cyx3705/2025-015/b-Picture/电器参考原理图.png

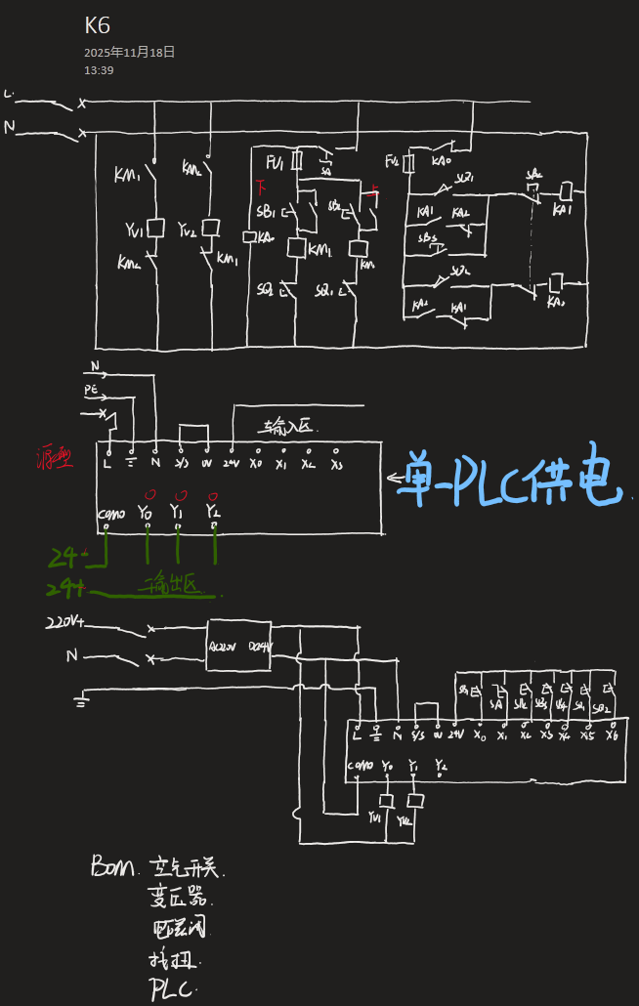
b-Picture/电器参考原理图.png
