cyx3705/2025-015/b-Picture/第三次作业图片记录 .png

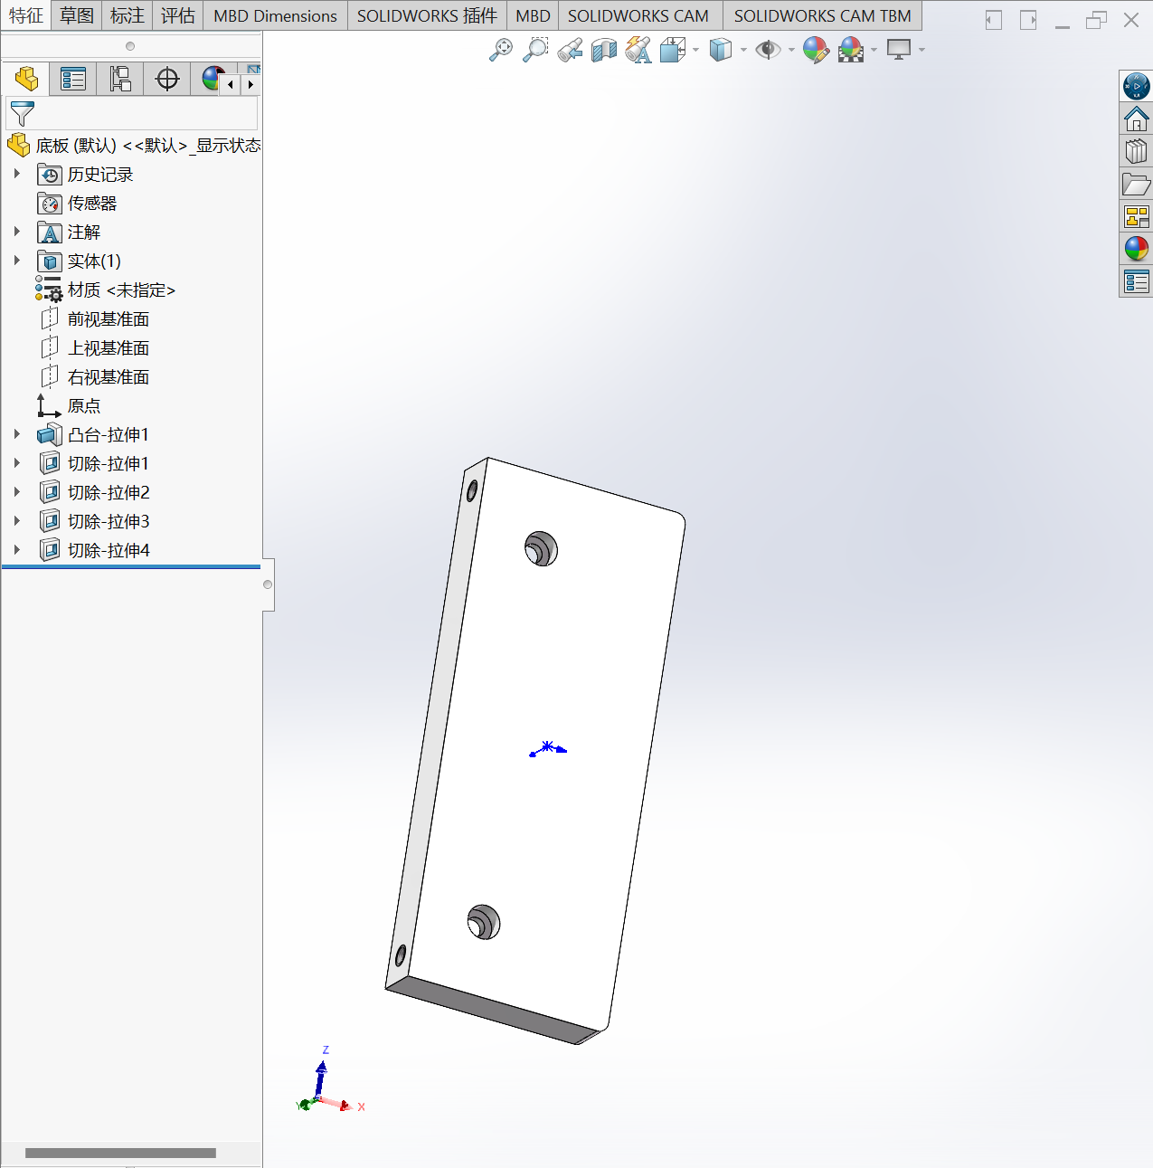
b-Picture/第三次作业图片记录 .png
