cyx3705/2025-015/b-Picture/第五次作业图片记录 (1).png

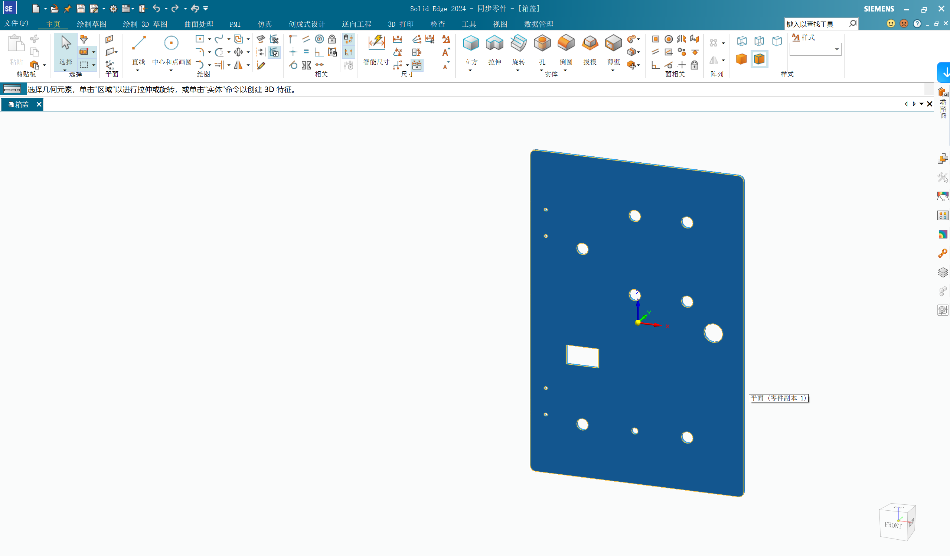
b-Picture/第五次作业图片记录 (1).png
