cyx3705/2025-015/b-Module-GE/按钮/NP2-BW1按钮三维模型202204.stp

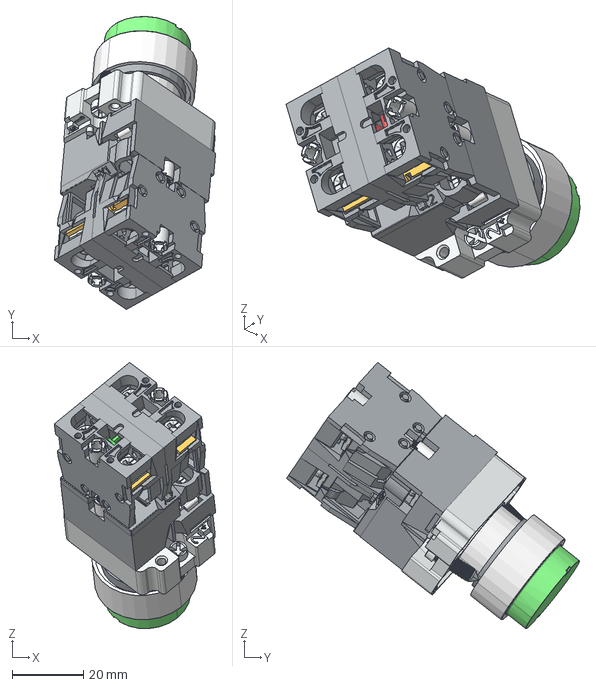
[picture p36: CAD file, 2026-09-21]
b-Module-GE/按钮/NP2-BW1按钮三维模型202204.stp
45.5 x 82.5 x 75.0 mm
