cyx3705/2025-015/b-Module-GE/配件箱/箱体.stp

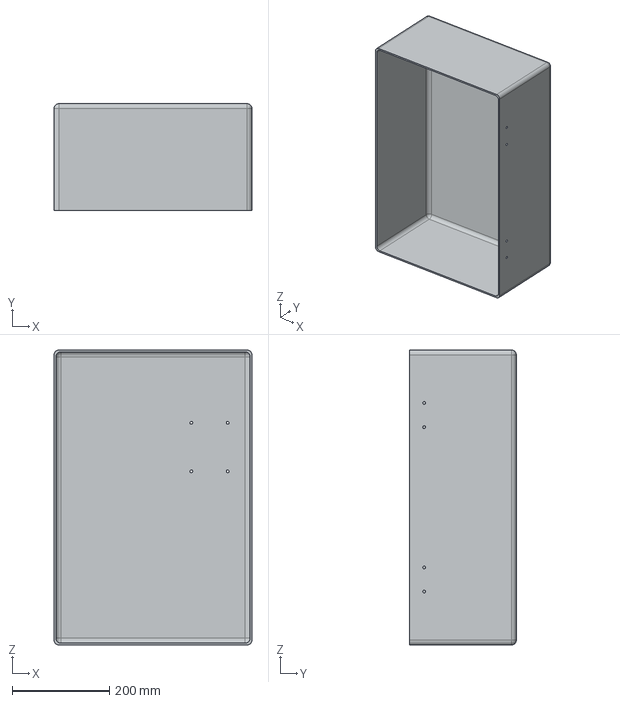
[picture p37: CAD file, 2026-09-21]
b-Module-GE/配件箱/箱体.stp
408.0 x 220.0 x 608.0 mm
