cyx3705/2025-015/b-Module-GE/零件1.stp

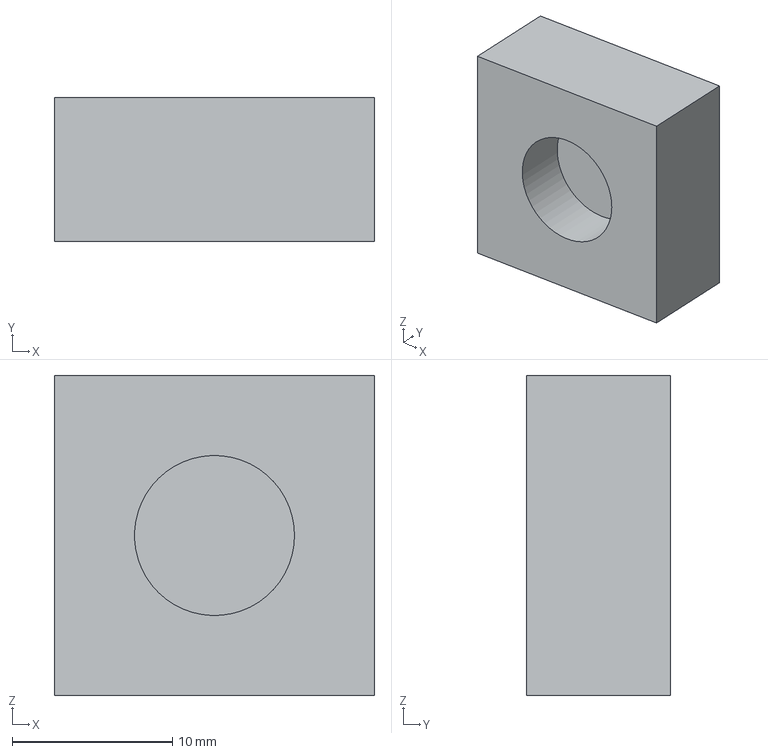
[picture p38: CAD file, 2026-09-21]
b-Module-GE/零件1.stp
20.0 x 9.00 x 20.0 mm
