cyx3705/2025-015/b-Module-SW/主体/背板.SLDPRT

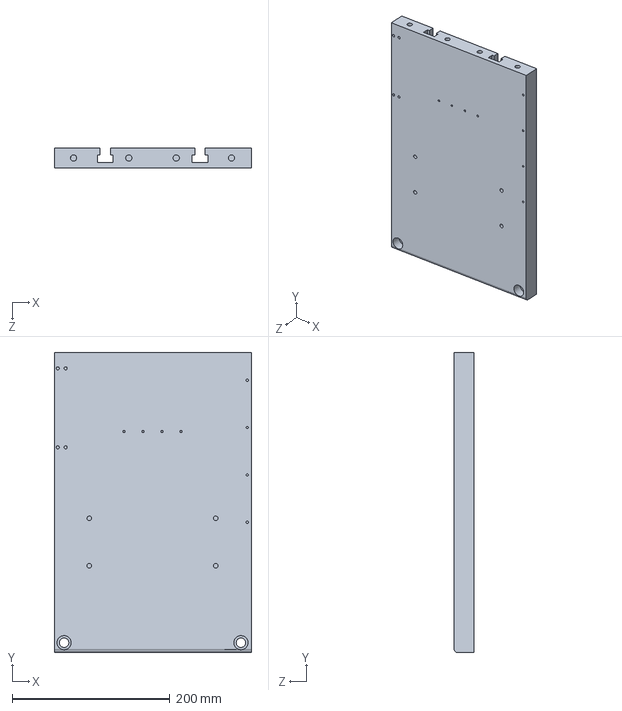
[picture p39: CAD file, 2026-05-30]
b-Module-SW/主体/背板.SLDPRT
250.0 x 380.0 x 25.0 mm
