cyx3705/2025-015/b-Module-GE/主体/光轴.STEP

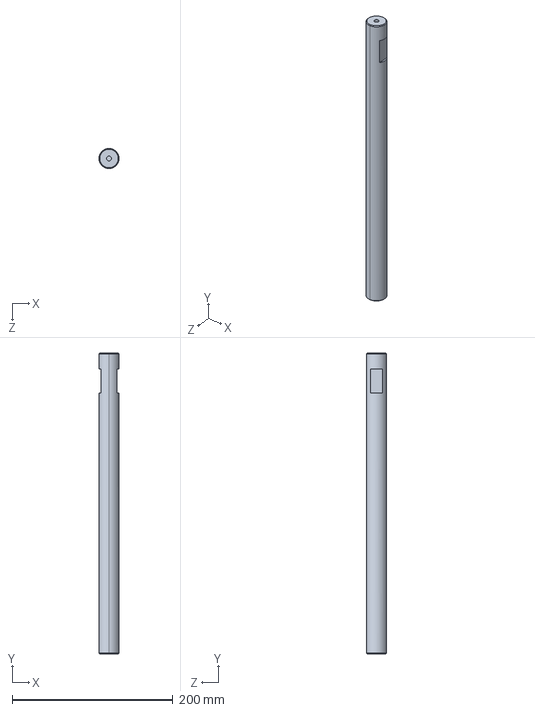
[picture p40: CAD file, 2026-09-21]
b-Module-GE/主体/光轴.STEP
25.0 x 375.0 x 25.0 mm
