cyx3705/2025-015/b-Module-GE/按钮/NP2-BW4按钮三维模型202204.stp

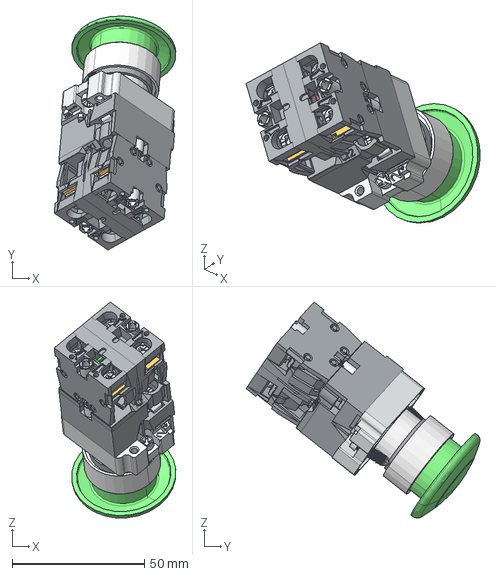
[picture p41: CAD file, 2026-09-21]
b-Module-GE/按钮/NP2-BW4按钮三维模型202204.stp
45.9 x 88.3 x 81.5 mm
