cyx3705/2025-015/b-Module-GE/触碰开关.stp

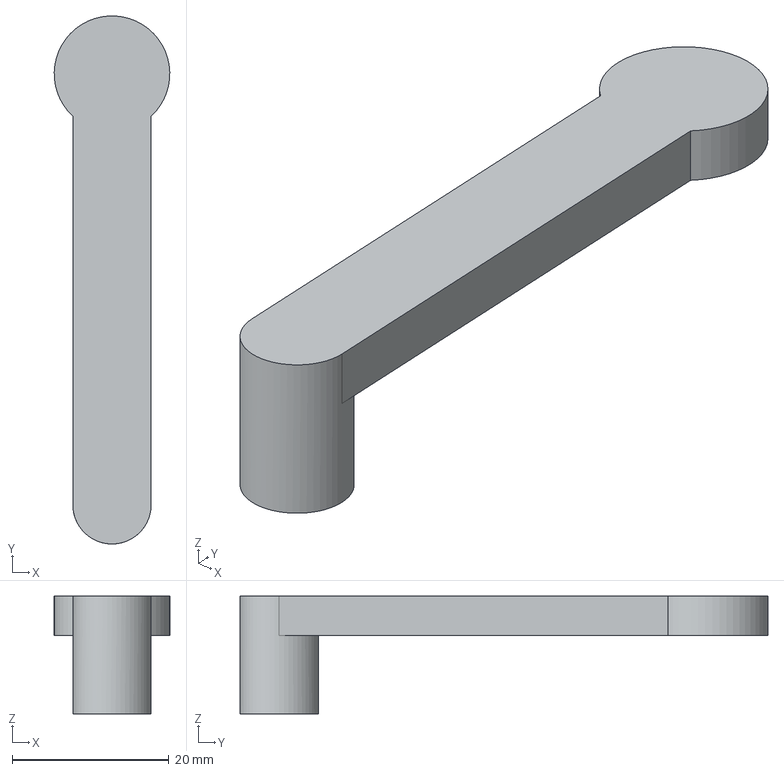
[picture p42: CAD file, 2026-09-21]
b-Module-GE/触碰开关.stp
14.7 x 67.4 x 15.0 mm
