cyx3705/2025-015/b-Module-GE/配件箱/保险丝座.stp

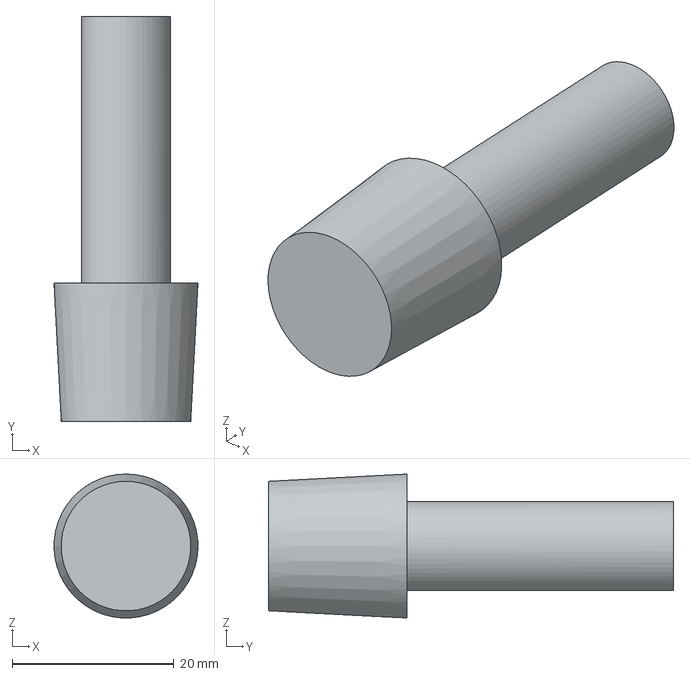
[picture p43: CAD file, 2026-09-21]
b-Module-GE/配件箱/保险丝座.stp
17.8 x 50.0 x 17.8 mm
