cyx3705/2025-015/b-Module-SW/主体/零件6.SLDPRT

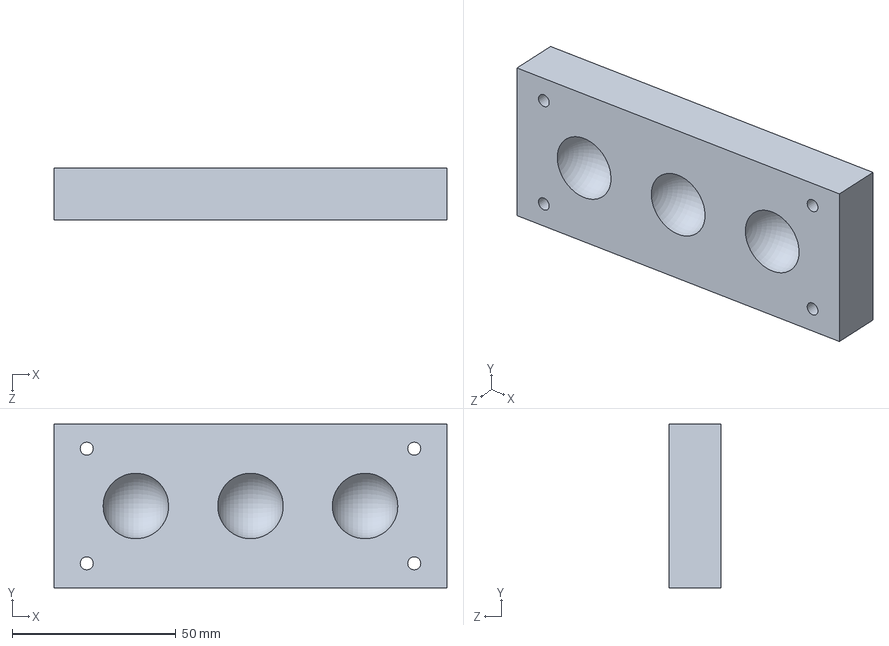
[picture p44: CAD file, 2026-05-30]
b-Module-SW/主体/零件6.SLDPRT
120.0 x 50.0 x 16.0 mm
