cyx3705/2025-015/b-Module-GE/专配体/锁芯.stp

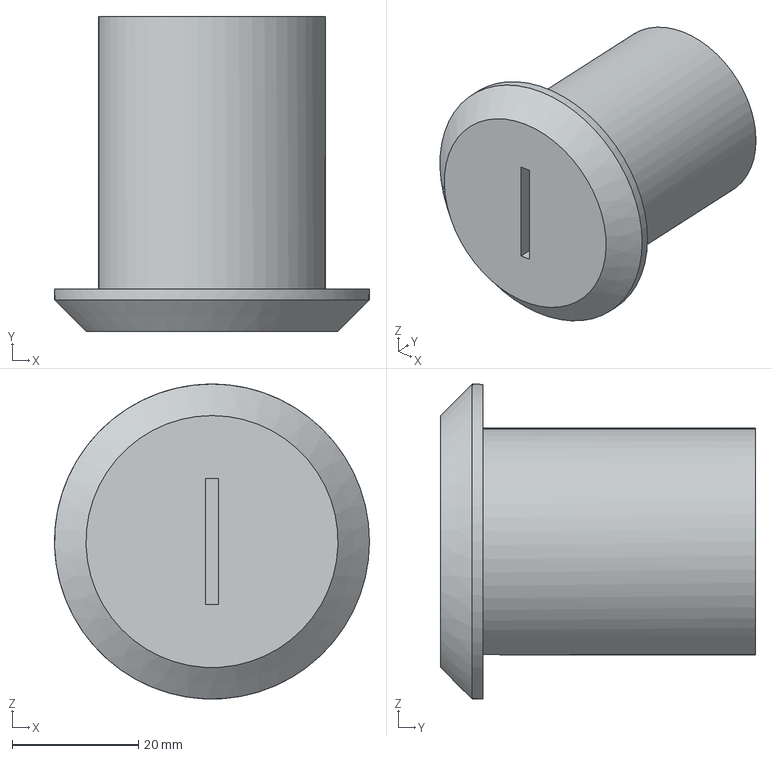
[picture p45: CAD file, 2026-09-21]
b-Module-GE/专配体/锁芯.stp
50.0 x 50.0 x 50.0 mm
