cyx3705/2025-015/b-Module-GE/导轨.stp

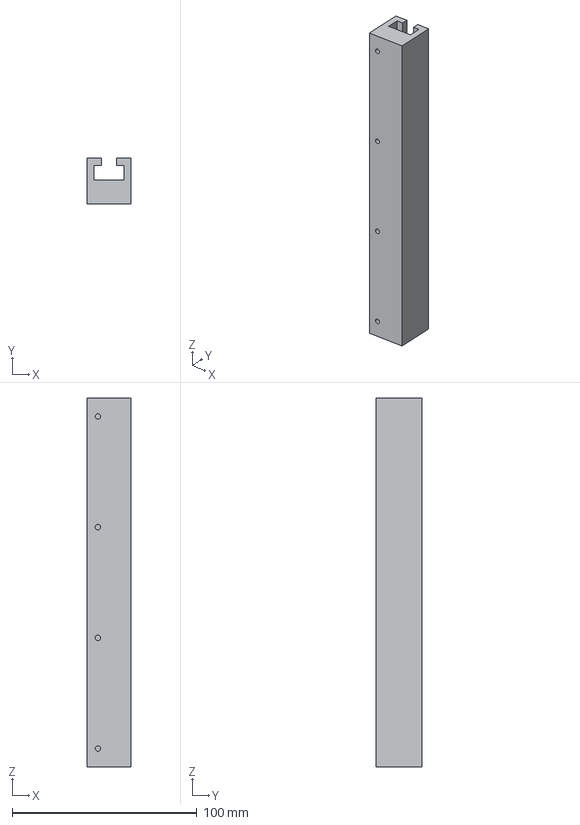
[picture p46: CAD file, 2026-09-21]
b-Module-GE/导轨.stp
24.0 x 25.0 x 200.0 mm
