cyx3705/2025-015/b-Module-SW/主体/工作版.SLDPRT

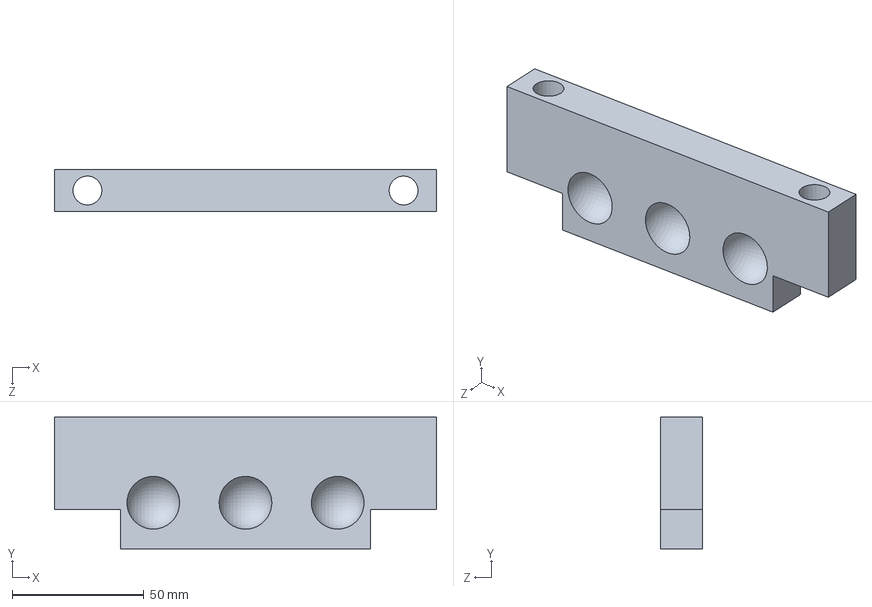
[picture p47: CAD file, 2026-05-30]
b-Module-SW/主体/工作版.SLDPRT
145.0 x 50.0 x 16.0 mm
