cyx3705/2025-015/b-Module-GE/主体/刚体固定架.stp

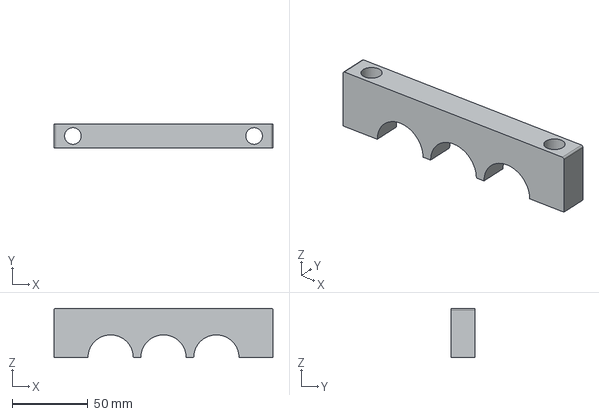
[picture p48: CAD file, 2026-09-21]
b-Module-GE/主体/刚体固定架.stp
145.0 x 16.0 x 32.5 mm
