cyx3705/2025-015/b-Module-GE/触碰开关盒.stp

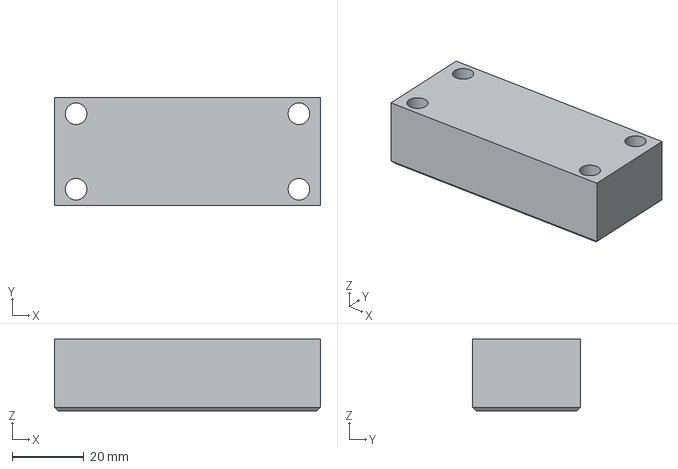
[picture p49: CAD file, 2026-09-21]
b-Module-GE/触碰开关盒.stp
74.0 x 30.0 x 20.0 mm
