cyx3705/2025-015/b-Module-GE/主体/底座支架.STEP

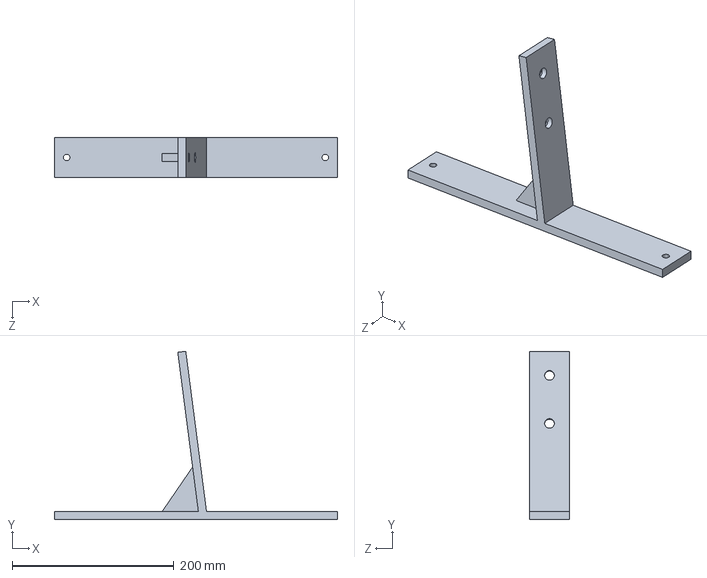
[picture p50: CAD file, 2026-09-21]
b-Module-GE/主体/底座支架.STEP
350.0 x 208.3 x 50.0 mm
