cyx3705/2025-015/b-Module-GE/滑块.stp

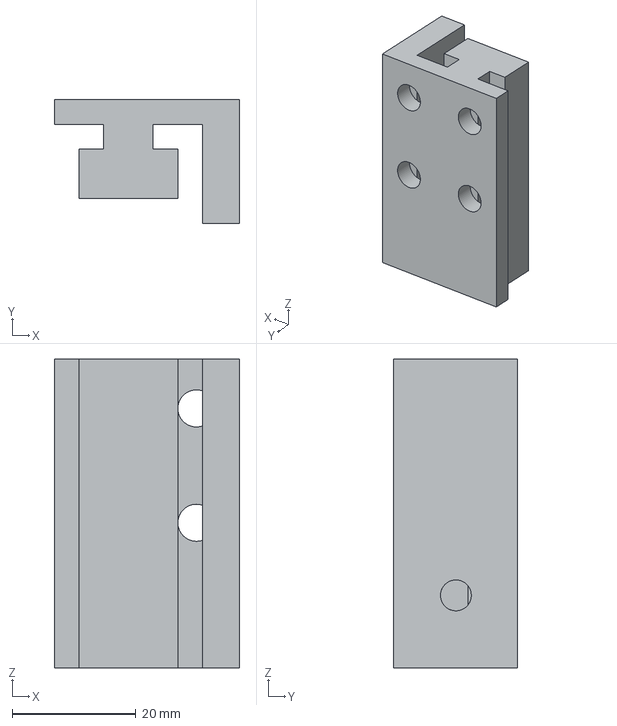
[picture p51: CAD file, 2026-09-21]
b-Module-GE/滑块.stp
30.0 x 20.0 x 50.0 mm
