cyx3705/2025-015/b-Module-GE/配件箱/箱盖.stp

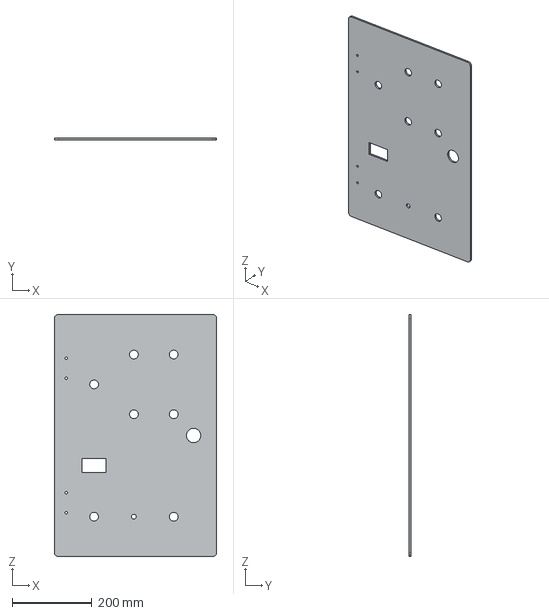
[picture p52: CAD file, 2026-09-21]
b-Module-GE/配件箱/箱盖.stp
408.0 x 5.00 x 608.0 mm
