cyx3705/2025-015/b-Module-SW/电盒支持架.SLDPRT

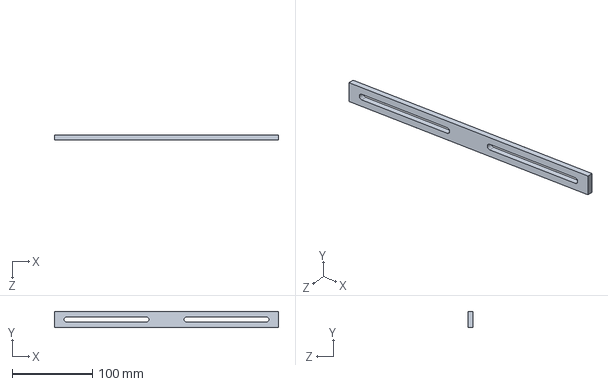
[picture p53: CAD file, 2026-05-30]
b-Module-SW/电盒支持架.SLDPRT
280.0 x 20.0 x 6.00 mm
