cyx3705/2025-015/b-Module-GE/主体/行程开关安专板.STEP

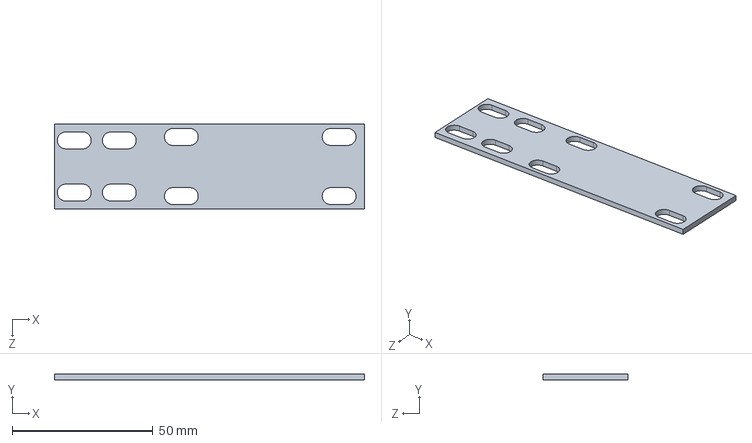
[picture p54: CAD file, 2026-09-21]
b-Module-GE/主体/行程开关安专板.STEP
110.0 x 2.00 x 30.0 mm
