cyx3705/2025-015/b-Module-GE/梯形螺母.stp

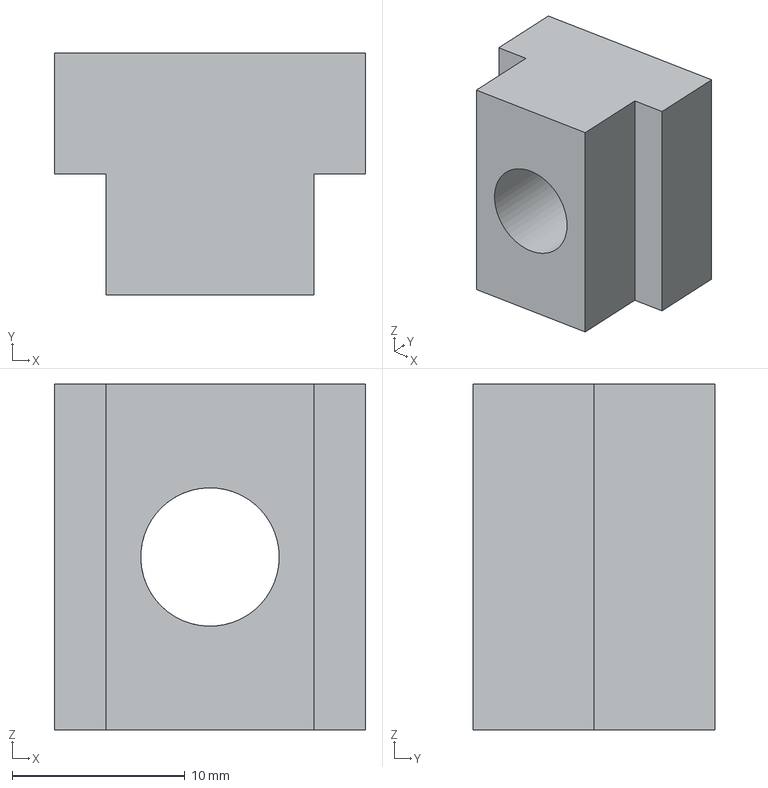
[picture p55: CAD file, 2026-09-21]
b-Module-GE/梯形螺母.stp
18.0 x 14.0 x 20.0 mm
