cyx3705/2025-015/b-Module-GE/专配体/顶板.STEP

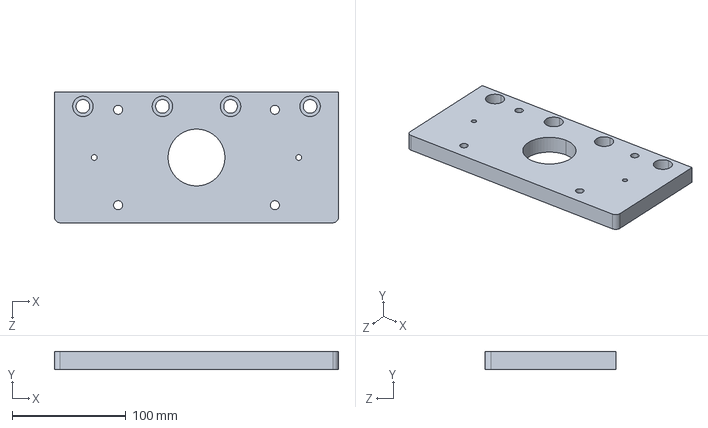
[picture p56: CAD file, 2026-09-21]
b-Module-GE/专配体/顶板.STEP
250.0 x 16.0 x 115.0 mm
