cyx3705/2025-015/b-Module-GE/主体/底板.STEP

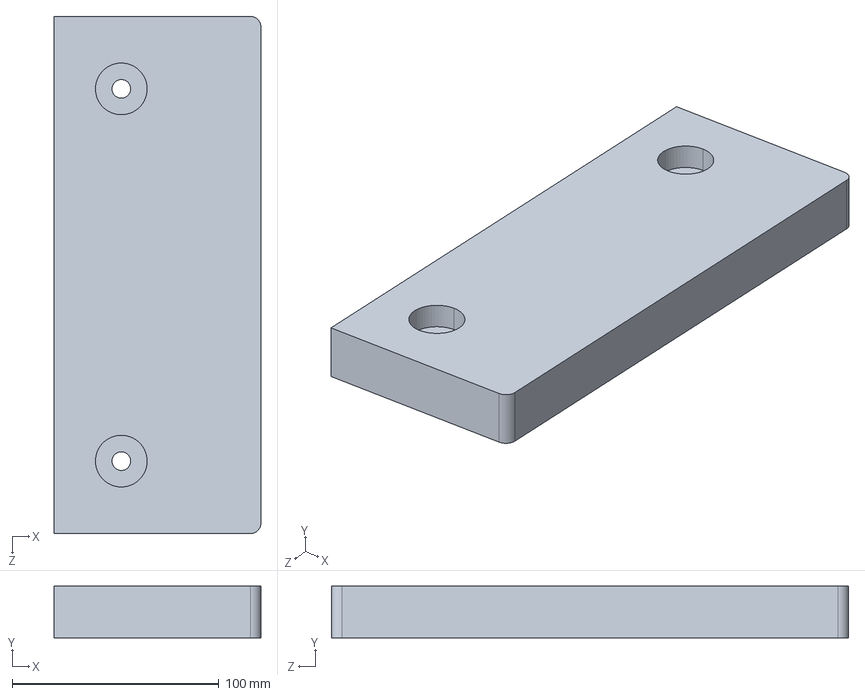
[picture p57: CAD file, 2026-09-21]
b-Module-GE/主体/底板.STEP
100.0 x 25.0 x 250.0 mm
