cyx3705/2025-015/b-Module-GE/气缸.STEP

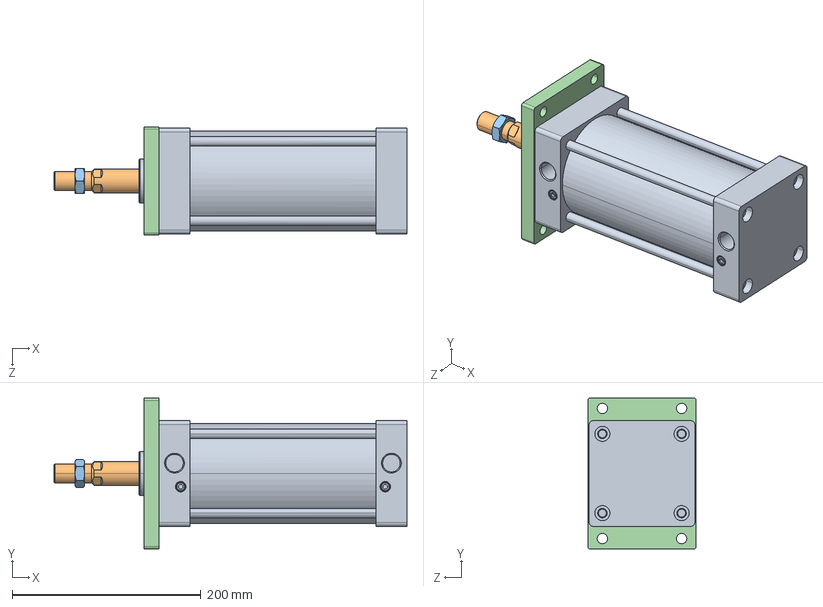
[picture p58: CAD file, 2026-09-21]
b-Module-GE/气缸.STEP
374.3 x 160.0 x 115.0 mm
SC100X150_c
SC-100x150-FA(0)_r
SC-100-M20x1.5 - Nut
F-SC100FA(SC)
SC-100 Screw x 4
