cyx3705/2025-015/b-Module-SW/滑块.SLDPRT

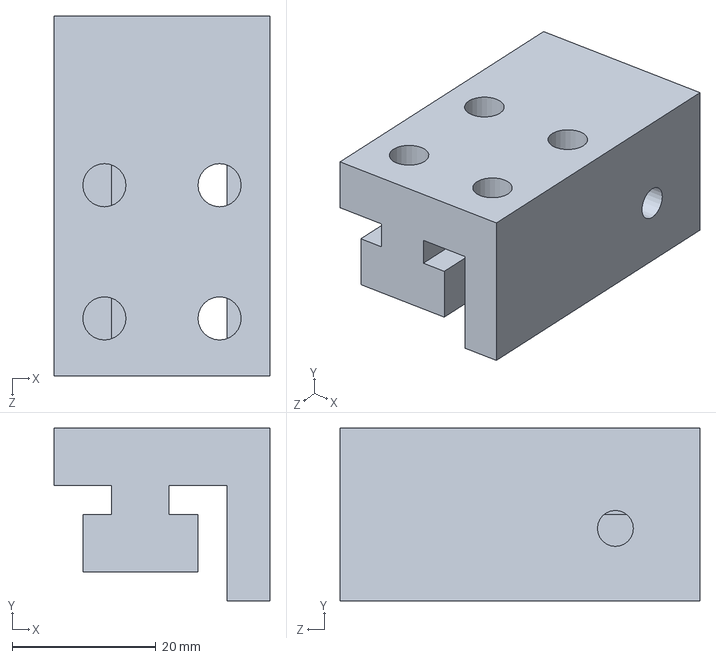
[picture p59: CAD file, 2026-05-30]
b-Module-SW/滑块.SLDPRT
30.0 x 24.0 x 50.0 mm
