cyx3705/2025-015/b-Module-SW/螺母.SLDPRT

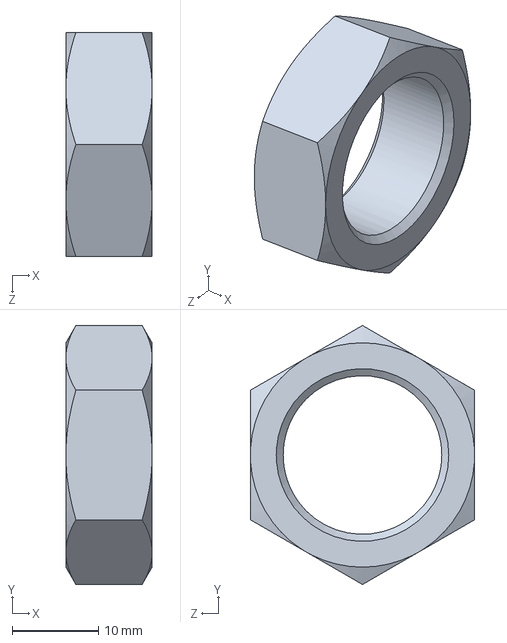
[picture p60: CAD file, 2026-05-30]
b-Module-SW/螺母.SLDPRT
10.0 x 30.0 x 26.0 mm
