cyx3705/2025-015/b-Module-SW/铜套.SLDPRT

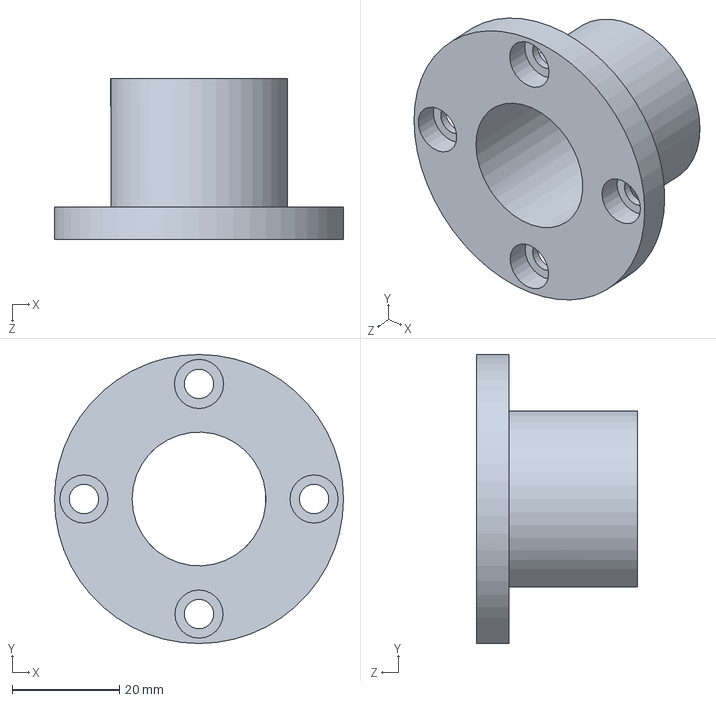
[picture p61: CAD file, 2026-05-30]
b-Module-SW/铜套.SLDPRT
54.0 x 54.0 x 30.0 mm
