cyx3705/2025-015/b-Module-SW/三联支架.SLDPRT

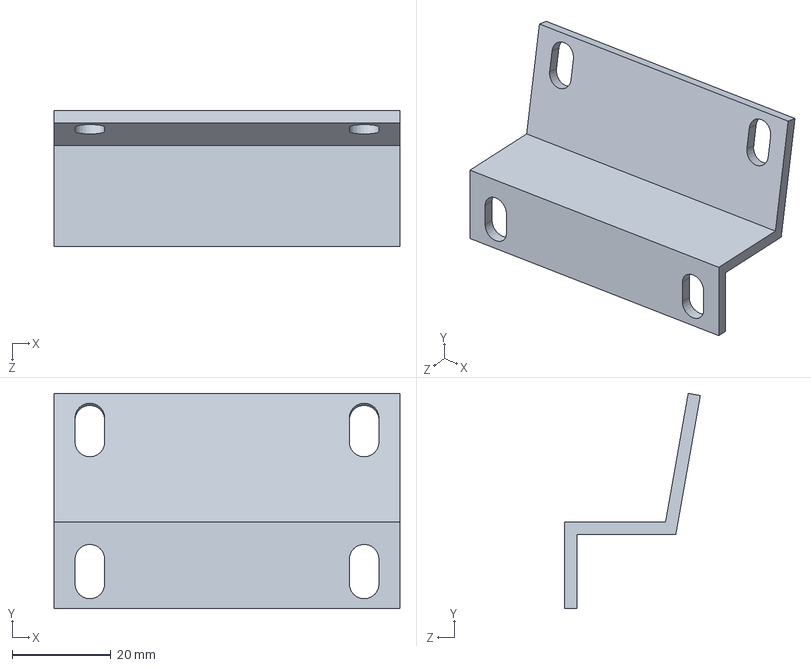
[picture p62: CAD file, 2026-05-30]
b-Module-SW/三联支架.SLDPRT
70.0 x 43.5 x 27.5 mm
