cyx3705/2025-015/b-Module-2D/顶板.pdf

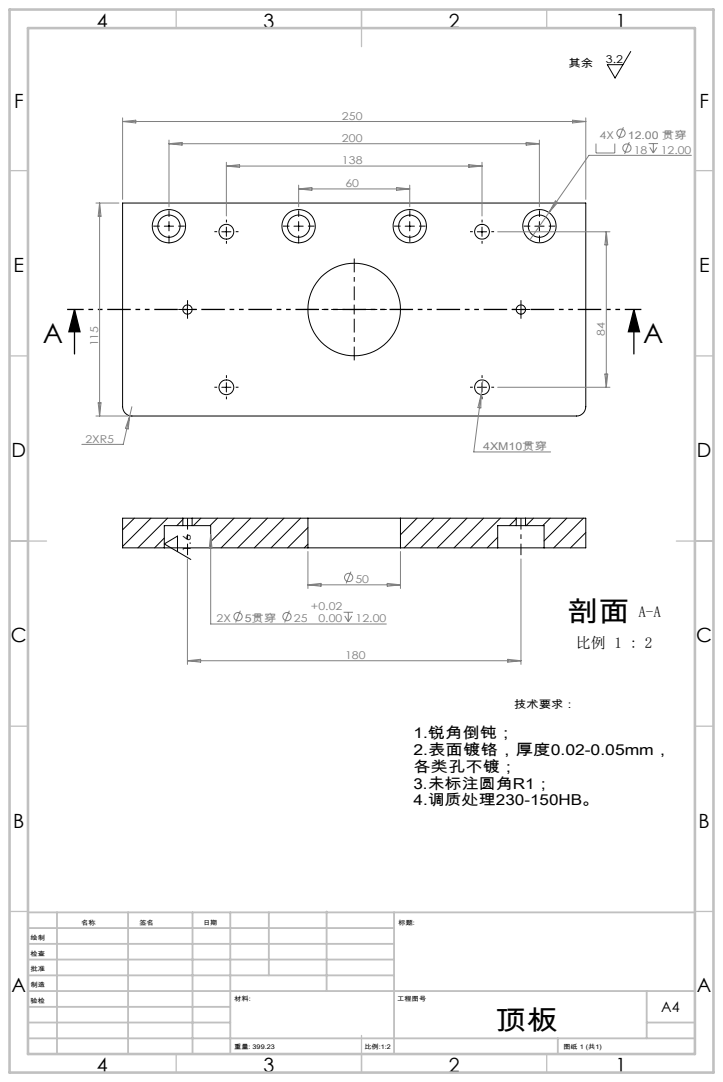
[picture p80: page 1]

绘制
检查
批准
制造
验检 | | | | 材料: | 工程图号 顶板 | A4
