cyx3705/2025-015/b-Office/接线图.pdf

-L1 1

-S1

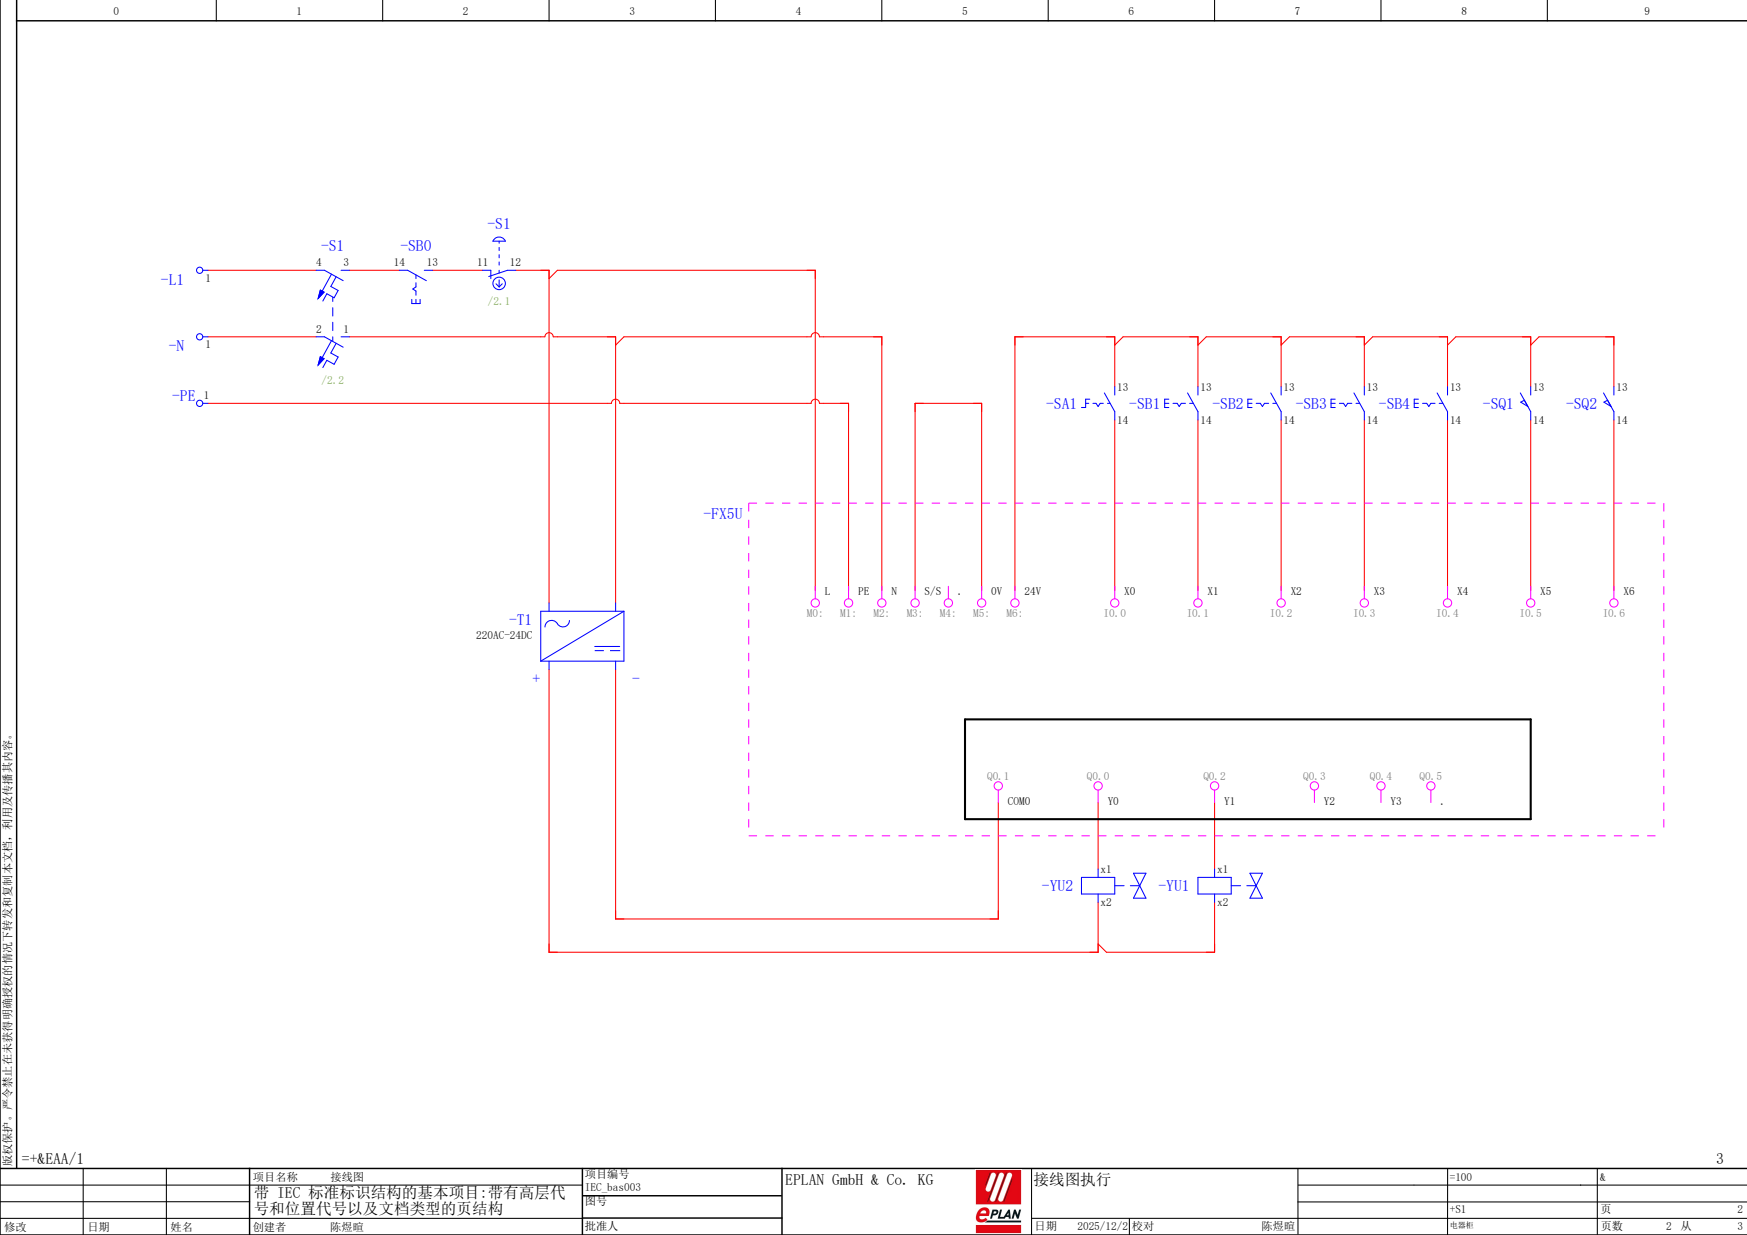
[picture p81: page 1]
=+&EAA/1; IEC_bas003; 陈煜暄; 接线图执行; 电器柜; 接线图; 批准人; 项目编号; 创建者; COM0

版权保护。严令禁止在未获得明确授权的情况下转发和复制本文档，利用及传播其内容。

项目名称
带 IEC 标准标识结构的基本项目:带有高层代
号和位置代号以及文档类型的页结构

EPLAN GmbH & Co. KG
